andi-makes/aWristWatch/firmware/api/chip/rtc.hpp

#pragma once

#include "exti.hpp"
#include "nvic.hpp"
#include "pwr.hpp"
#include "rcc.hpp"

#include <bits.hpp>
#include <cinttypes>
#include <fields.hpp>
#include <register.hpp>

struct RTC {
    static constexpr zol::addr_t address = 0x4000'2800;

    using TR       = zol::reg<uint32_t, address + 0x0>;
    using DR       = zol::reg<uint32_t, address + 0x4>;
    using CR       = zol::reg<uint32_t, address + 0x8>;
    using ISR      = zol::reg<uint32_t, address + 0xC>;
    using PRER     = zol::reg<uint32_t, address + 0x10>;
    using WUTR     = zol::reg<uint32_t, address + 0x14>;
    using ALRMAR   = zol::reg<uint32_t, address + 0x1C>;
    using ALRMBR   = zol::reg<uint32_t, address + 0x20>;
    using WPR      = zol::reg<uint32_t, address + 0x24>;
    using SSR      = zol::reg<uint32_t, address + 0x28>;
    using SHIFTR   = zol::reg<uint32_t, address + 0x2C>;
    using TSTR     = zol::reg<uint32_t, address + 0x30>;
    using TSDR     = zol::reg<uint32_t, address + 0x34>;
    using TSSSR    = zol::reg<uint32_t, address + 0x38>;
    using CALR     = zol::reg<uint32_t, address + 0x3C>;
    using TAMPCR   = zol::reg<uint32_t, address + 0x40>;
    using ALRMASSR = zol::reg<uint32_t, address + 0x44>;
    using ALRMBSSR = zol::reg<uint32_t, address + 0x48>;
    using OR       = zol::reg<uint32_t, address + 0x4C>;
    using BKP0R    = zol::reg<uint32_t, address + 0x50>;
    using BKP1R    = zol::reg<uint32_t, address + 0x54>;
    using BKP2R    = zol::reg<uint32_t, address + 0x58>;
    using BKP3R    = zol::reg<uint32_t, address + 0x5C>;
    using BKP4R    = zol::reg<uint32_t, address + 0x60>;

    // CR
    struct cr {
        using COE     = zol::bit_rw<CR, 23>;
        using OSEL    = zol::field_rw<CR, 21, 2>;
        using POL     = zol::bit_rw<CR, 20>;
        using COSEL   = zol::bit_rw<CR, 19>;
        using BKP     = zol::bit_rw<CR, 18>;
        using SUB1H   = zol::bit_w<CR, 17>;
        using ADD1H   = zol::bit_w<CR, 16>;
        using TSIE    = zol::bit_rw<CR, 15>;
        using WUTIE   = zol::bit_rw<CR, 14>;
        using ALRBIE  = zol::bit_rw<CR, 13>;
        using ALRAIE  = zol::bit_rw<CR, 12>;
        using TSE     = zol::bit_rw<CR, 11>;
        using WUTE    = zol::bit_rw<CR, 10>;
        using ALRBE   = zol::bit_rw<CR, 9>;
        using ALRAE   = zol::bit_rw<CR, 8>;
        using FMT     = zol::bit_rw<CR, 6>;
        using BYPSHAD = zol::bit_rw<CR, 5>;
        using REFCKON = zol::bit_rw<CR, 4>;
        using TSEDGE  = zol::bit_rw<CR, 3>;
        using WUCKSEL = zol::field_rw<CR, 0, 3>;

        cr() = delete;
    };

    struct isr {
        using RECALPF = zol::bit_r<ISR, 16>;
        using TAMP3F  = zol::bit_rc0<ISR, 15>;
        using TAMP2F  = zol::bit_rc0<ISR, 14>;
        using TAMP1F  = zol::bit_rc0<ISR, 13>;
        using TSOVF   = zol::bit_rc0<ISR, 12>;
        using TSF     = zol::bit_rc0<ISR, 11>;
        using WUTF    = zol::bit_rc0<ISR, 10>;
        using ALRBF   = zol::bit_rc0<ISR, 9>;
        using ALRAF   = zol::bit_rc0<ISR, 8>;
        using INIT    = zol::bit_rw<ISR, 7>;
        using INITF   = zol::bit_r<ISR, 6>;
        using RSF     = zol::bit_rc0<ISR, 5>;
        using INITS   = zol::bit_r<ISR, 4>;
        using SHPF    = zol::bit_r<ISR, 3>;
        using WUTWF   = zol::bit_r<ISR, 2>;
        using ALRBWF  = zol::bit_r<ISR, 1>;
        using ALRAWF  = zol::bit_r<ISR, 0>;

        isr() = delete;
    };

    struct prer {
        using PREDIV_A = zol::field_rw<PRER, 16, 7>;
        using PREDIV_S = zol::field_rw<PRER, 0, 15>;

        prer() = delete;
    };

    [[gnu::always_inline]] static inline void disable_write_protect() {
        WPR::set_reg(0xCAu);
        WPR::set_reg(0x53U);
    }

    [[gnu::always_inline]] static inline void enable_write_protect() {
        WPR::set_reg(0xFFu);
    }

    static void power_on() {
        PWR::power_on();
        PWR::set(PWR::cr::DBP);    // Disable backup write protection

        // RCC::CSR::set_bit(8);				   // CSR_LSEON
        RCC::csr::LSEON::write(on);
        while (RCC::csr::LSERDY::read() == 0) {    // CSR_LSERDY
        }

        // RCC::CSR::set_bit(16);	  // RTCSEL (select LSE clock)
        RCC::csr::RTCSEL::set(1U);
    }

    static void enable() { RCC::csr::RTCEN::write(on); }

    static void set_time(TR::type_t hrs, TR::type_t min, TR::type_t sec) {
        disable_write_protect();
        // Enter initialization mode
        // ISR::set_bit(7);
        isr::INIT::write(on);
        // Wait until registers can be updated
        // while (ISR::get_bit(6) == 0) {
        while (isr::INITF::read() == false) {
        }

        // Update time
        TR::set_reg(sec | (min << 8) | (hrs << 16));

        // Exit initialization mode
        // ISR::clear_bit(7);
        isr::INIT::write(off);

        enable_write_protect();
    }

    static void set_date(DR::type_t date, DR::type_t month, DR::type_t year) {
        disable_write_protect();
        // Enter initialization mode
        // ISR::set_bit(7);
        isr::INIT::write(on);
        // Wait until registers can be updated
        // while (ISR::get_bit(6) == 0) {
        while (isr::INITF::read() == false) {
        }

        // Update date
        DR::set_reg(date | (month << 8) | (year << 16));

        // Exit initialization mode
        // ISR::clear_bit(7);
        isr::INIT::write(off);

        enable_write_protect();
    }

    static void set_time_and_date(TR::type_t hrs,
                                  TR::type_t min,
                                  TR::type_t sec,
                                  DR::type_t date,
                                  DR::type_t month,
                                  DR::type_t year) {
        disable_write_protect();
        // Enter initialization mode
        // ISR::set_bit(7);
        isr::INIT::write(on);
        // Wait until registers can be updated
        // while (ISR::get_bit(6) == 0) {
        while (isr::INITF::read() == false) {
        }

        // Update time
        TR::set_reg(sec | (min << 8) | (hrs << 16));

        // Update date
        DR::set_reg(date | (month << 8) | (year << 16));

        // Exit initialization mode
        // ISR::clear_bit(7);
        isr::INIT::write(off);

        enable_write_protect();
    }

    static bool is_initialized() { return isr::INITS::read(); }

    static void setup_wakeup_timer(WUTR::type_t wut, CR::type_t wucksel) {
        disable_write_protect();
        cr::WUTE::write(off);
        while (isr::WUTWF::read() == 0) {    // WUTWF
        }
        // 1023 ==> 0.5sec
        // 511  ==> 0.25sec
        // 255  ==> 0.125sec
        WUTR::set_reg(wut);
        cr::WUCKSEL::set(wucksel);
        cr::WUTE::write(on);

        EXTI::IMR::set_bit(20U);
        EXTI::RTSR::set_bit(20U);

        NVIC::ISER::set_bit(2U);

        cr::WUTIE::write(on);
        enable_write_protect();
    }

    RTC() = delete;
};
